darekb/tempHumidityPressureCollector/IMG_20161004_230553.jpg

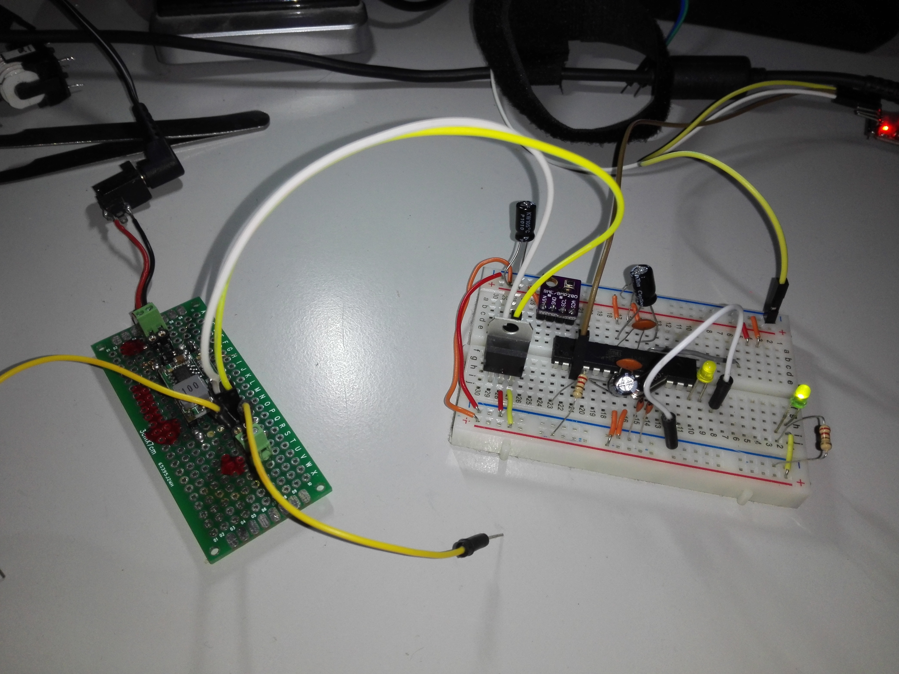
IMG_20161004_230553.jpg
